jbilander/Par2Ser/cpld/rtl/par2ser_fsm.v

// =============================================================================
//  par2ser_fsm.v -- Transaction FSM, one-hot encoded for the ispMACH 4000.
//
//  One-hot encoding: every state is its own flop, every state test is a
//  single wire (no 4-bit AND tree). On a CPLD that's product-term bound,
//  this typically reduces pterms enough to free macrocells -- exactly what
//  we need to fit all three LEDs.
//
//  CRITICAL one-hot discipline: for each state bit, the next-state
//  expression is ALWAYS:
//
//      state[N] <= (enter_from_X if cond_X) | (enter_from_Y if cond_Y)
//                  | (state[N] & ~any_exit_condition)
//
//  The 'state[N] & ~exits' term is what makes the state STICKY -- without
//  it, every "waiting" state would clear itself after one cycle and the
//  FSM would die. (This is exactly what bit a previous one-hot attempt:
//  it omitted the stay terms and fit beautifully, but the FSM didn't work.)
//
//  Behavior is preserved bit-for-bit from the binary FSM that was tested
//  in WinUAE with the par2ser.device driver.
// =============================================================================

module par2ser_fsm (
    input  wire        clk,
    input  wire        reset,

    input  wire        req_assert,
    input  wire        req_deassert,
    input  wire        pout_edge,
    input  wire [7:0]  amiga_d_in,

    output reg         drive_amiga_d,
    output reg  [7:0]  amiga_d_out,
    output reg         drive_busy,
    output reg         drive_ack,

    input  wire        ft_rxf_n,
    input  wire        ft_txe_n,
    input  wire [7:0]  ft_d_in,

    output reg         ft_wr_pulse,
    output reg         ft_rd_pulse,
    output reg         drive_ft_d,
    output reg  [7:0]  ft_d_out,

    output wire        led_tx_pulse,
    output wire        led_rx_pulse,
    output wire        led_act_state,
    output wire        siwu_n           // FT240X Send Immediate, active low
);

    // One-hot state bit indices.
    localparam
        S_IDLE         = 0,
        S_DECODE       = 1,
        S_WRITE_WAIT   = 2,
        S_WRITE_LATCH  = 3,
        S_WRITE_FT     = 4,
        S_READ_FETCH   = 5,
        S_READ_PRESENT = 6,
        S_DRAIN        = 7,
        S_CTRL         = 8;

    reg [8:0] state;
    reg [6:0] byte_count;

    // Common sub-expressions, each a single wire.
    wire has_data  = ~ft_rxf_n;
    wire can_write = ~ft_txe_n;
    wire is_write  = ~amiga_d_in[7] & ~amiga_d_in[6];   // D7=0, D6=0 -> WRITE1
    wire is_read   = ~amiga_d_in[7] &  amiga_d_in[6];   // D7=0, D6=1 -> READ1
    wire is_drain  =  amiga_d_in[7] & ~amiga_d_in[6];   // D7=1, D6=0 -> READ2/WRITE2 (drains)
    wire is_ctrl   =  amiga_d_in[7] &  amiga_d_in[6];   // D7=1, D6=1 -> control cmd
    wire bc_zero   = (byte_count == 7'd0);

    // -------------------------------------------------------------------------
    //  State register -- per-bit next-state. Each bit:
    //     state[N] <= (entry conditions) | (state[N] & ~exit conditions)
    //  This preserves bit-for-bit the binary FSM's transitions.
    // -------------------------------------------------------------------------
    always @(posedge clk) begin
        if (reset) begin
            state <= 9'b000000001;   // IDLE
        end else begin
            state[S_IDLE]         <= (state[S_IDLE]         & ~req_assert)
                                   | (state[S_WRITE_WAIT]   &  req_deassert)
                                   | (state[S_READ_FETCH]   &  req_deassert)
                                   | (state[S_READ_PRESENT] &  req_deassert)
                                   | (state[S_DRAIN]        &  req_deassert)
                                   | (state[S_CTRL]         &  req_deassert);

            state[S_DECODE]       <= (state[S_IDLE]         &  req_assert);
                                    // DECODE always transitions out in one cycle, no hold term.

            state[S_WRITE_WAIT]   <= (state[S_DECODE]       &  is_write)
                                   | (state[S_WRITE_FT]     & ~bc_zero)
                                   | (state[S_WRITE_WAIT]   & ~req_deassert & ~pout_edge);

            state[S_WRITE_LATCH]  <= (state[S_WRITE_WAIT]   & ~req_deassert &  pout_edge)
                                   | (state[S_WRITE_LATCH]  & ~can_write);

            state[S_WRITE_FT]     <= (state[S_WRITE_LATCH]  &  can_write);
                                    // WRITE_FT always transitions out in one cycle, no hold term.

            // READ path, reworked for correct handshake semantics (see note at
            // the data-path section below). PRESENT = waiting for the Amiga's
            // POUT edge; FETCH = one FT240X read per edge. The byte counter is
            // NOT used on the read side: the Amiga toggles exactly `size`
            // times and then deasserts SELECT, so the edge count IS the byte
            // count and bc terms here would be redundant product terms.
            state[S_READ_FETCH]   <= (state[S_READ_PRESENT] & ~req_deassert &  pout_edge)
                                   | (state[S_READ_FETCH]   & ~req_deassert & ~has_data);

            state[S_READ_PRESENT] <= (state[S_DECODE]       &  is_read)
                                   | (state[S_READ_FETCH]   & ~req_deassert &  has_data)
                                   | (state[S_READ_PRESENT] & ~req_deassert & ~pout_edge);

            state[S_DRAIN]        <= (state[S_DECODE]       &  is_drain)
                                   | (state[S_WRITE_FT]     &  bc_zero)
                                   | (state[S_DRAIN]        & ~req_deassert);

            state[S_CTRL]         <= (state[S_DECODE]       &  is_ctrl)
                                   | (state[S_CTRL]         & ~req_deassert);
        end
    end

    // -------------------------------------------------------------------------
    //  Byte counter -- single-condition enables, same as binary version.
    // -------------------------------------------------------------------------
    wire count_load = state[S_DECODE] & ~amiga_d_in[7];
    wire count_dec  = (state[S_WRITE_FT]     & ~bc_zero);   // write side only;
                      // the read side needs no counter (edges = bytes).

    always @(posedge clk) begin
        if (reset)           byte_count <= 7'd0;
        else if (count_load) byte_count <= {1'b0, amiga_d_in[5:0]};
        else if (count_dec)  byte_count <= byte_count - 1'b1;
    end

    // -------------------------------------------------------------------------
    //  Data path -- unchanged from binary version (already optimal).
    // -------------------------------------------------------------------------
    always @(posedge clk) ft_d_out <= amiga_d_in;

    // Capture the FT240X byte at the clock edge that ENDS the RD# pulse --
    // while RD# is still low and the FT is still driving its bus. RD# is low
    // for one 83ns cycle; FT240X data is valid ~50ns after RD# falls, giving
    // ~30ns of setup at the capture edge. The previous rd_capture register
    // sampled one cycle AFTER RD# released, when the FT had already let go
    // of the bus (hold <= 14ns) -- reading a released bus.
    always @(posedge clk) if (ft_rd_pulse) amiga_d_out <= ft_d_in;

    // -------------------------------------------------------------------------
    //  Output registers -- now driven from single-wire state[N] signals.
    // -------------------------------------------------------------------------
    always @(posedge clk) begin
        if (reset) begin
            drive_busy    <= 1'b0;
            drive_amiga_d <= 1'b0;
            drive_ft_d    <= 1'b0;
            ft_wr_pulse   <= 1'b0;
            ft_rd_pulse   <= 1'b0;
            drive_ack     <= 1'b0;
        end else begin
            drive_busy    <= ~state[S_IDLE];
            // Drive the Amiga data bus only from the FIRST completed fetch
            // onward, holding through the rest of the read, and release on
            // SELECT deassert. Never drive before the Amiga's first POUT
            // edge: the Amiga is still driving the bus (DDRB=0xff) for
            // several microseconds after asserting SELECT, and the old
            // `drive on READ_PRESENT` asserted ~400ns in -- microseconds of
            // 8-line bus contention against the CIA on every READ1 (the
            // prime crash suspect: a glitched CIA-A can flip /OVL). The
            // first POUT toggle is the Amiga's guarantee that it has
            // tristated (DDRB=0 always precedes the read loop).
            drive_amiga_d <= ~req_deassert &
                             ( (state[S_READ_FETCH] & has_data)
                             | (drive_amiga_d & (state[S_READ_FETCH]
                                               | state[S_READ_PRESENT])) );
            // Drive the FT data bus one cycle EARLIER (S_WRITE_LATCH) and hold it
            // through S_WRITE_FT, so the bus is valid before, during, and after the
            // ft_wr_pulse (which fires in the S_WRITE_FT cycle). The FT240X latches on
            // WR's falling edge; previously drive_ft_d asserted a cycle too late and WR
            // strobed a high-Z bus, latching garbage. See timing note below.
            drive_ft_d    <=  state[S_WRITE_LATCH] | state[S_WRITE_FT];
            ft_wr_pulse   <=  state[S_WRITE_LATCH] & can_write;
            ft_rd_pulse   <=  state[S_READ_FETCH]  & has_data & ~req_deassert;
            drive_ack     <=  state[S_IDLE]        & has_data;
        end
    end

    // -------------------------------------------------------------------------
    //  LED outputs -- free decodes of existing signals.
    // -------------------------------------------------------------------------
    assign led_act_state = ~state[S_IDLE];
    assign led_tx_pulse  =  drive_ft_d;       // lit while we drive FT bus
    assign led_rx_pulse  =  drive_amiga_d;    // lit while we drive Amiga bus

    // -------------------------------------------------------------------------
    //  FT240X Send Immediate (SIWU#) -- active low, asserted during any CTRL
    //  command. A CTRL command (D7=1, D6=1 in the command byte) is the
    //  Amiga's way of saying "flush the FT240X TX buffer to USB now".
    //  S_CTRL is entered on the CTRL command and persists until req_deassert,
    //  so SIWU# is held low for the entire command duration -- the FT240X
    //  acts on the falling edge and the held-low time is harmless. Single
    //  combinational decode -- cheap.
    // -------------------------------------------------------------------------
    assign siwu_n = ~state[S_CTRL];

endmodule
